UnexpectedMaker/esp32s3/3d models/OMGS3/OMGS3.jpg

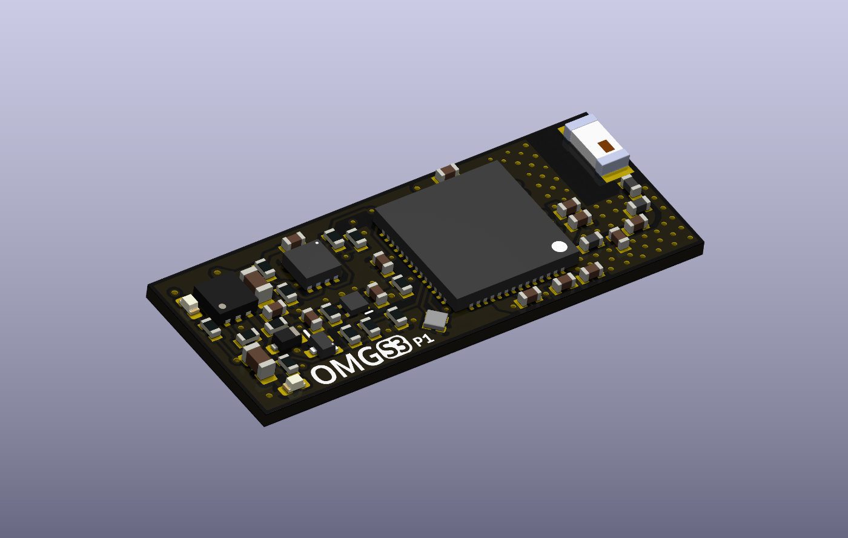
3d models/OMGS3/OMGS3.jpg
