UnexpectedMaker/esp32s3/Pinout Cards/FeatherS3Neo_Pin_Reference.png

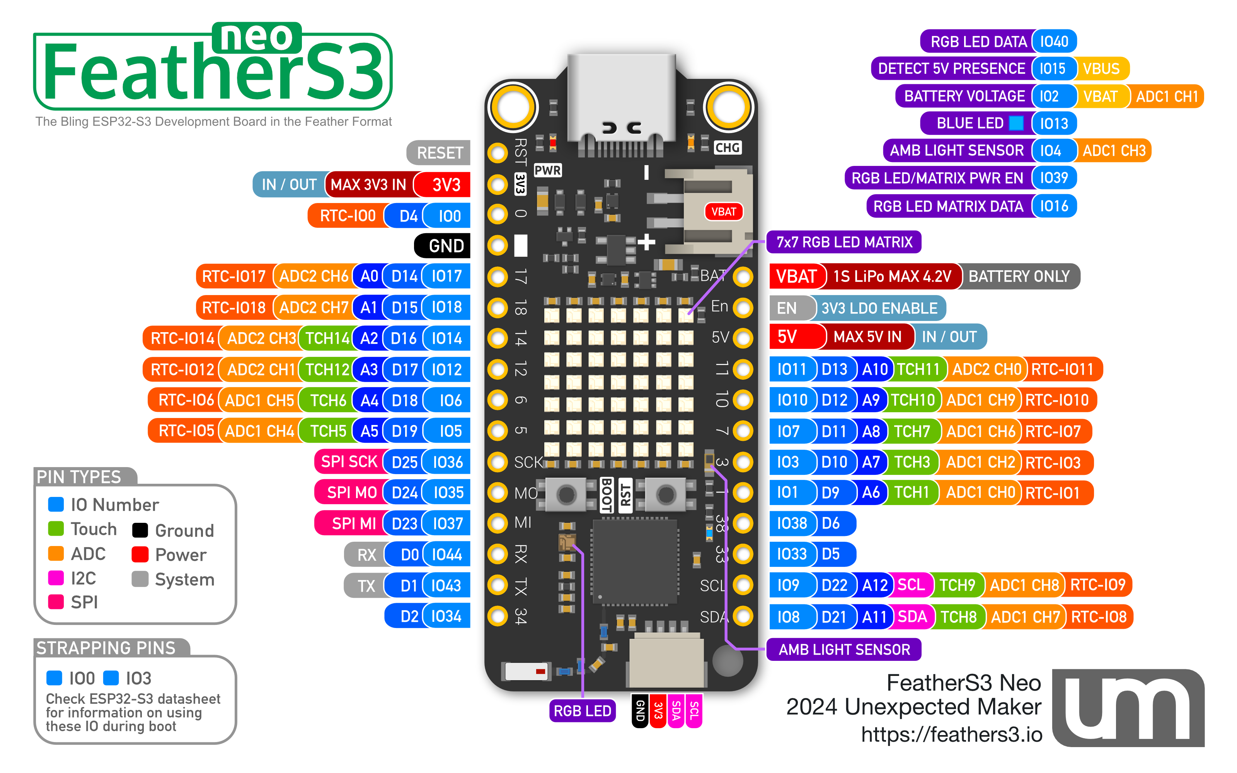
Pinout Cards/FeatherS3Neo_Pin_Reference.png
