UnexpectedMaker/esp32s3/Pinout Cards/NanoS3_Pin_Reference.png

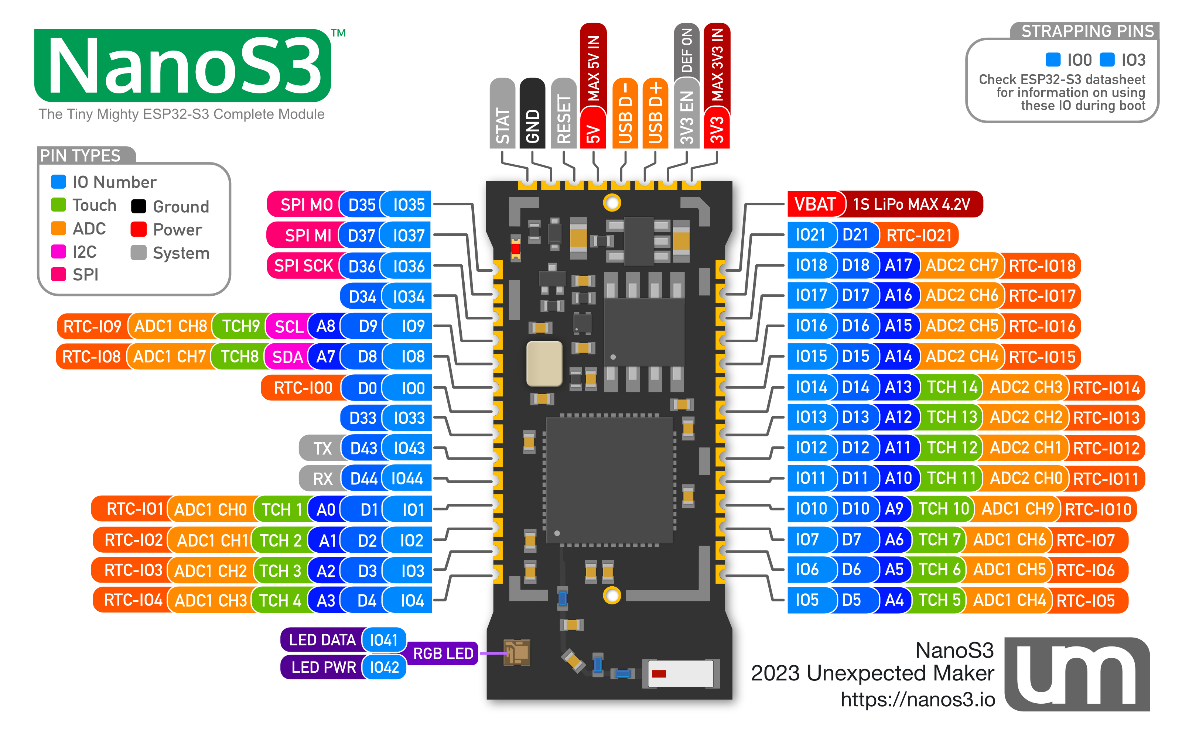
Pinout Cards/NanoS3_Pin_Reference.png
