UnexpectedMaker/esp32s3/series_d/pinout_cards/feathers3d_pinout.jpg

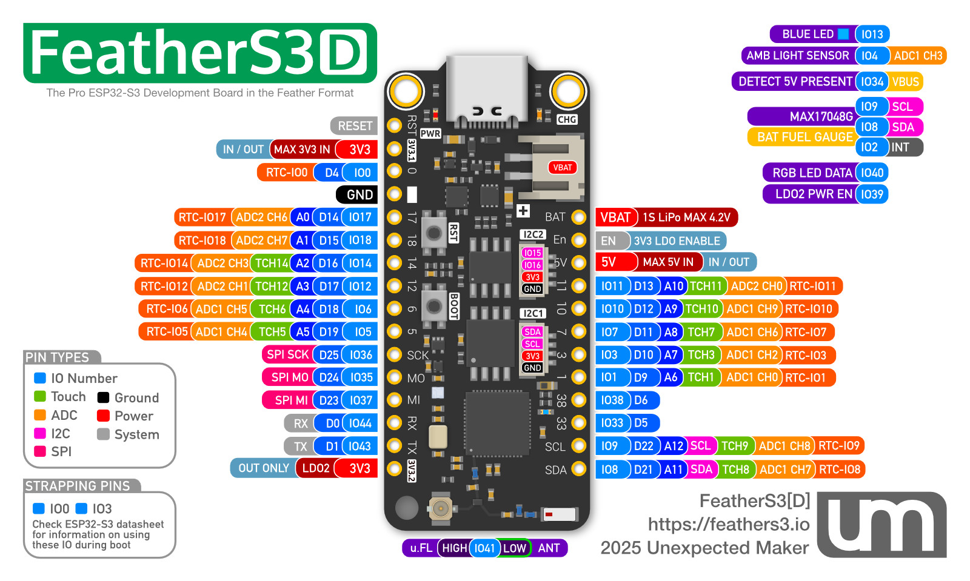
series_d/pinout_cards/feathers3d_pinout.jpg
