UnexpectedMaker/esp32s3/series_d/pinout_cards/pros3d_pinout.jpg

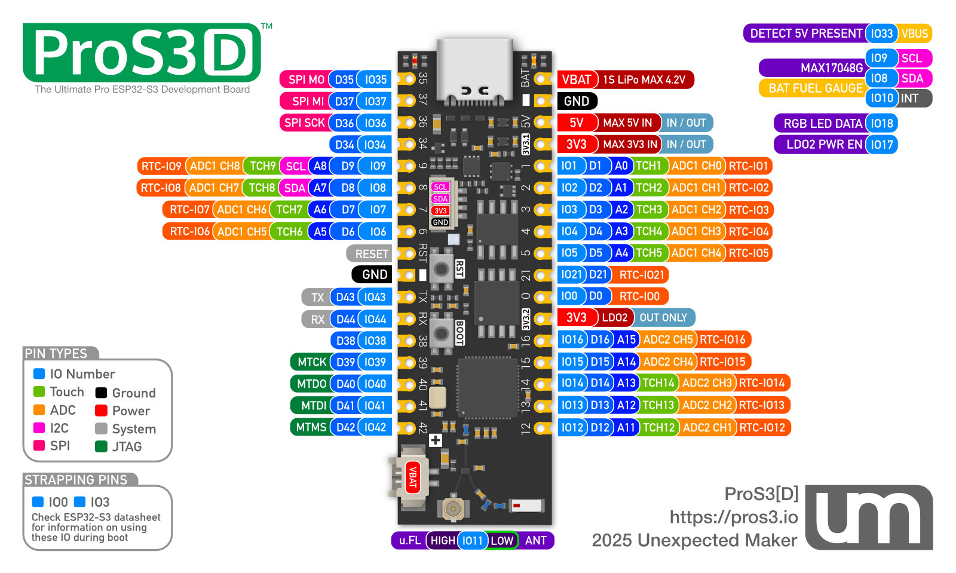
series_d/pinout_cards/pros3d_pinout.jpg
