UnexpectedMaker/esp32s3/code/circuitpython/shipping files/feathers3/feathers3.py

#FeatherS3 Helper Library
# 2022 Seon Rozenblum, Unexpected Maker
#
# Project home:
#   https://feathers3.io
#

# Import required libraries
import time
import board
from digitalio import DigitalInOut, Direction, Pull
from analogio import AnalogIn

# Init Blink LED
led13 = DigitalInOut(board.LED)
led13.direction = Direction.OUTPUT

# Init LDO2 Pin
ldo2 = DigitalInOut(board.LDO2)
ldo2.direction = Direction.OUTPUT

# Setup the BATTERY voltage sense pin
vbat_voltage = AnalogIn(board.BATTERY)

# Setup the VBUS sense pin
vbus_sense = DigitalInOut(board.VBUS_SENSE)
vbus_sense.direction = Direction.INPUT

   
# Helper functions

def led_blink():
    """Set the internal LED IO13 to it's inverse state"""
    led13.value = not led13.value

def led_set( state ):
    """Set the internal LED IO13 to this state"""
    led13.value = state

def set_ldo2_power(state):
    """Enable or Disable power to the onboard NeoPixel to either show colour, or to reduce power fro deep sleep."""
    global ldo2
    ldo2.value = state
    
def get_battery_voltage():
    """Get the approximate battery voltage."""
    # This formula should show the nominal 4.2V max capacity (approximately) when 5V is present and the
    # VBAT is in charge state for a 1S LiPo battery with a max capacity of 4.2V   
    global vbat_voltage
    ADC_RESOLUTION = 2 ** 16 -1
    AREF_VOLTAGE = 3.3
    R1 = 442000
    R2 = 160000
    return (vbat_voltage.value/ADC_RESOLUTION*AREF_VOLTAGE*(R1+R2)/R2)

def get_vbus_present():
    """Detect if VBUS (5V) power source is present"""
    global vbus_sense
    return vbus_sense.value

def rgb_color_wheel(wheel_pos):
    """Color wheel to allow for cycling through the rainbow of RGB colors."""
    wheel_pos = wheel_pos % 255

    if wheel_pos < 85:
        return 255 - wheel_pos * 3, 0, wheel_pos * 3
    elif wheel_pos < 170:
        wheel_pos -= 85
        return 0, wheel_pos * 3, 255 - wheel_pos * 3
    else:
        wheel_pos -= 170
        return wheel_pos * 3, 255 - wheel_pos * 3, 0
    
